DanEfran/Skiff/references/circuitry examples/power supply as in mfos wallwartschematicpage1.gif

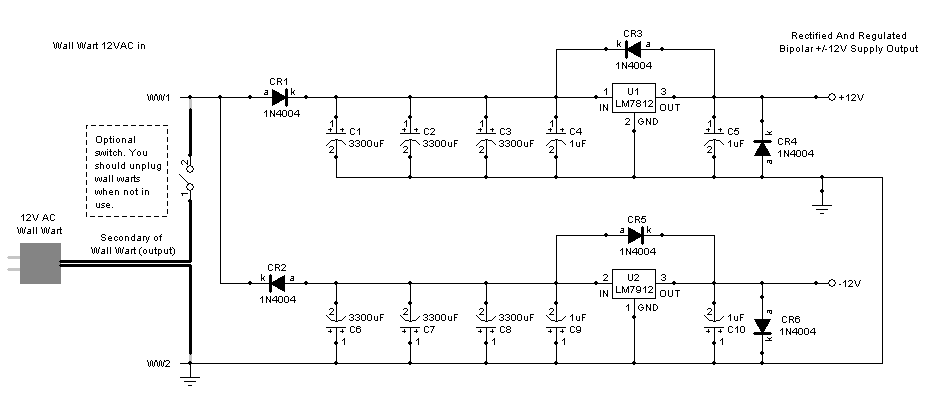
references/circuitry examples/power supply as in mfos wallwartschematicpage1.gif
