DanEfran/Skiff/references/dimensions/1u module dimensions 35495_2314_1u_specs_2_1.jpg

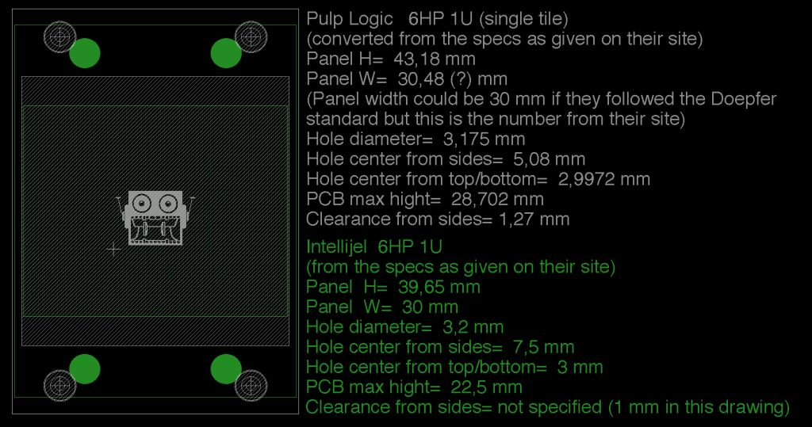
references/dimensions/1u module dimensions 35495_2314_1u_specs_2_1.jpg
