DanEfran/Skiff/references/EuroSynth - MIDI Interfacing_files/pointer-right.jpg

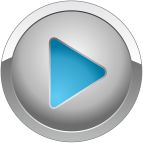
references/EuroSynth - MIDI Interfacing_files/pointer-right.jpg
