DanEfran/Skiff/references/EuroSynth - Signal Specification_files/jack-black.jpg

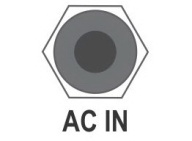
references/EuroSynth - Signal Specification_files/jack-black.jpg
