DanEfran/Skiff/references/EuroSynth - Signal Specification_files/jack-grey.jpg

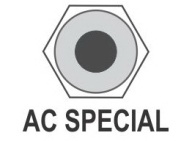
references/EuroSynth - Signal Specification_files/jack-grey.jpg
