DanEfran/Skiff/references/EuroSynth - Signal Specification_files/jack-orange.jpg

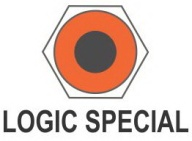
references/EuroSynth - Signal Specification_files/jack-orange.jpg
