DanEfran/Skiff/references/EuroSynth - Signal Specification_files/jack-purple.jpg

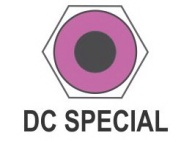
references/EuroSynth - Signal Specification_files/jack-purple.jpg
