DanEfran/Skiff/references/EuroSynth - Signal Specification_files/jack-yellow.jpg

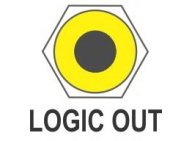
references/EuroSynth - Signal Specification_files/jack-yellow.jpg
