DanEfran/Skiff/first modules/MIDI Input/skiff_MIDI_in/display.h

// display.h
// skiff_MIDI_in
#ifndef SKIFF_MIDI_IN_DISPLAY_H
#define SKIFF_MIDI_IN_DISPLAY_H


void initDisplay(void);
void testClearScreen();
void testlines();
void testfastlines();
void testroundrects();
void tftPrintTest();


#endif // SKIFF_MIDI_IN_DISPLAY_H
